grob6000/hpbattery/20231212_114950.jpg

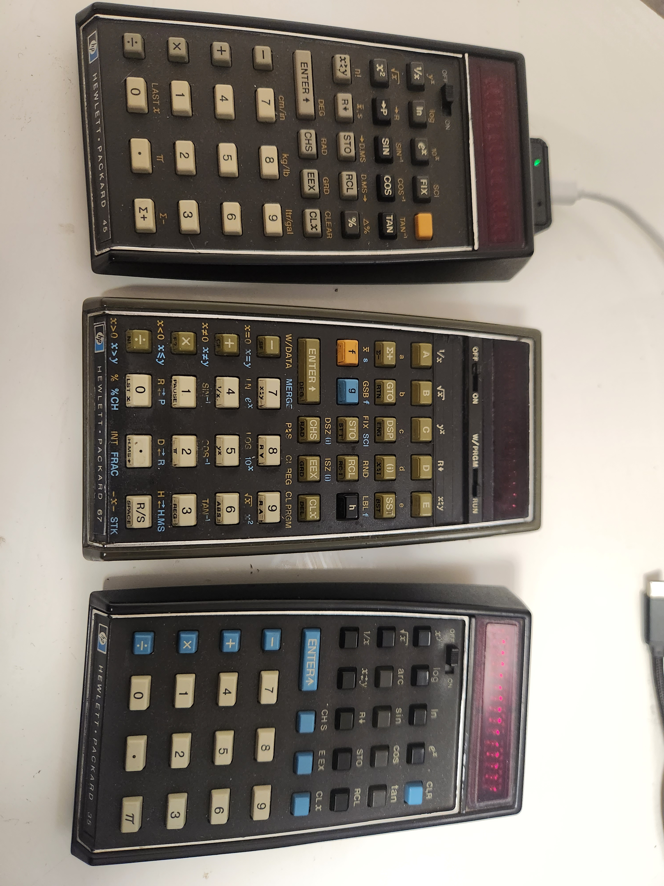
20231212_114950.jpg
