grob6000/hpbattery/20231212_115047.jpg

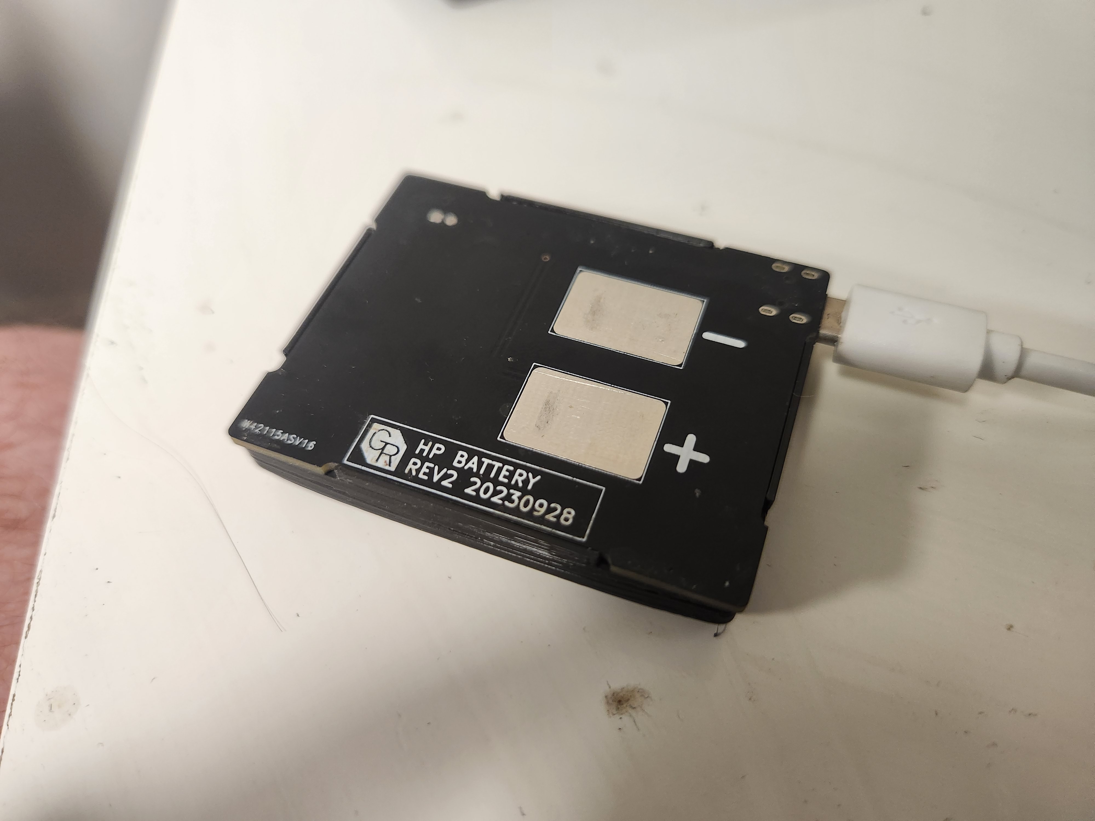
20231212_115047.jpg
