grob6000/hpbattery/20231212_115104.jpg

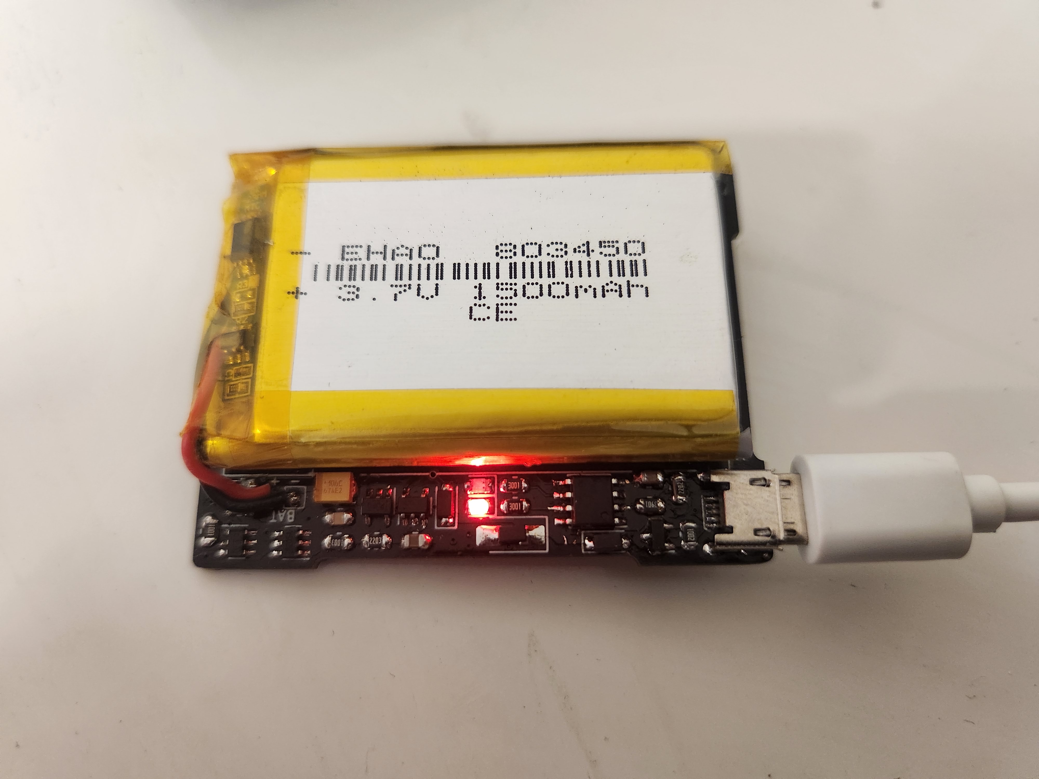
20231212_115104.jpg
