grob6000/hpbattery/20231212_115130.jpg

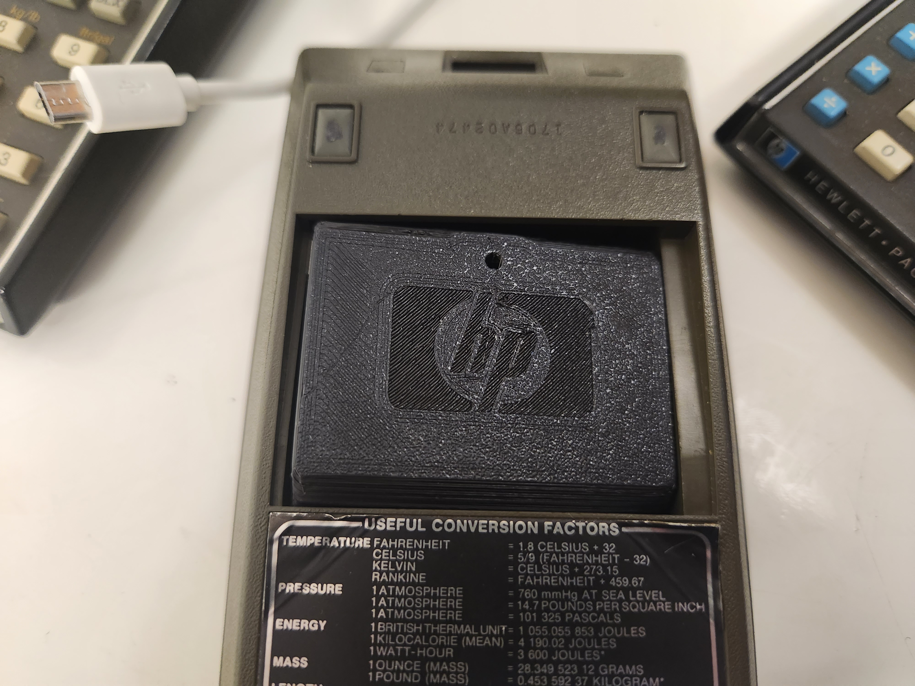
20231212_115130.jpg
